PicoNexus/sao-dev-board/IMAGES/DSC_1120.jpg

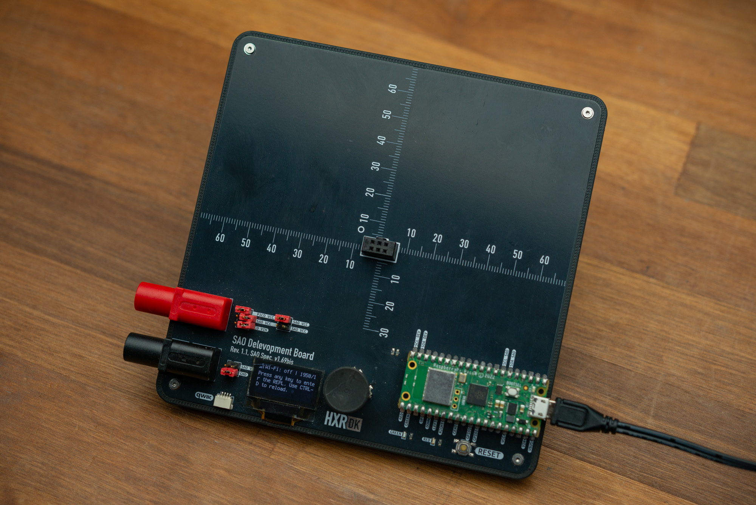
IMAGES/DSC_1120.jpg
